silardg/VESA-ESP/Docs/Images/IMG_1075.jpg

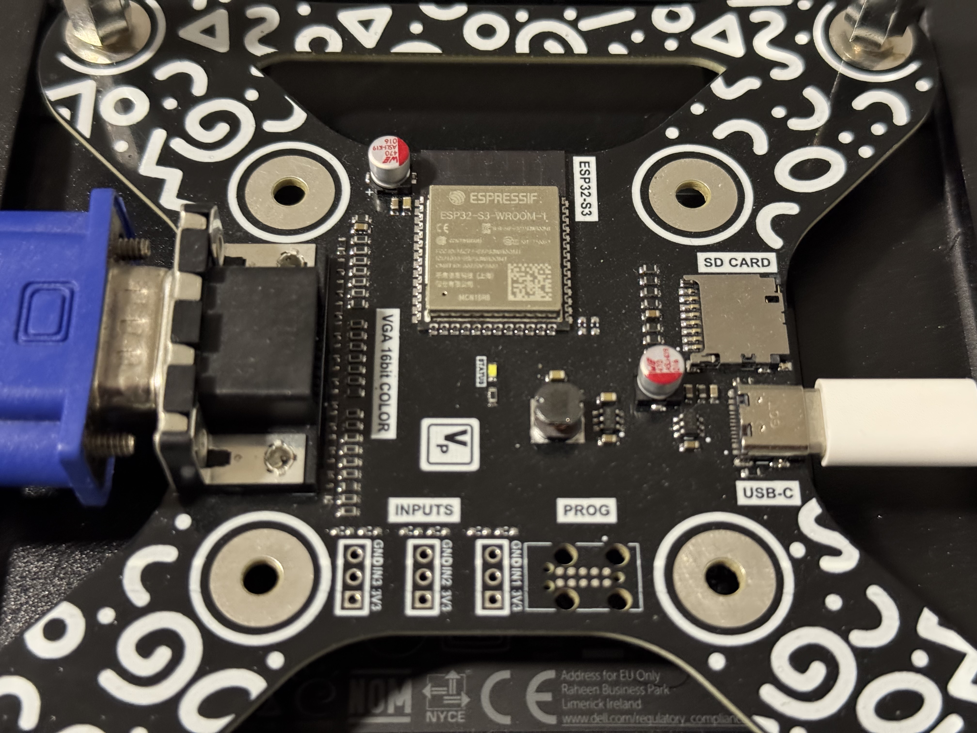
Docs/Images/IMG_1075.jpg
