silardg/VESA-ESP/Docs/Images/IMG_1078.jpg

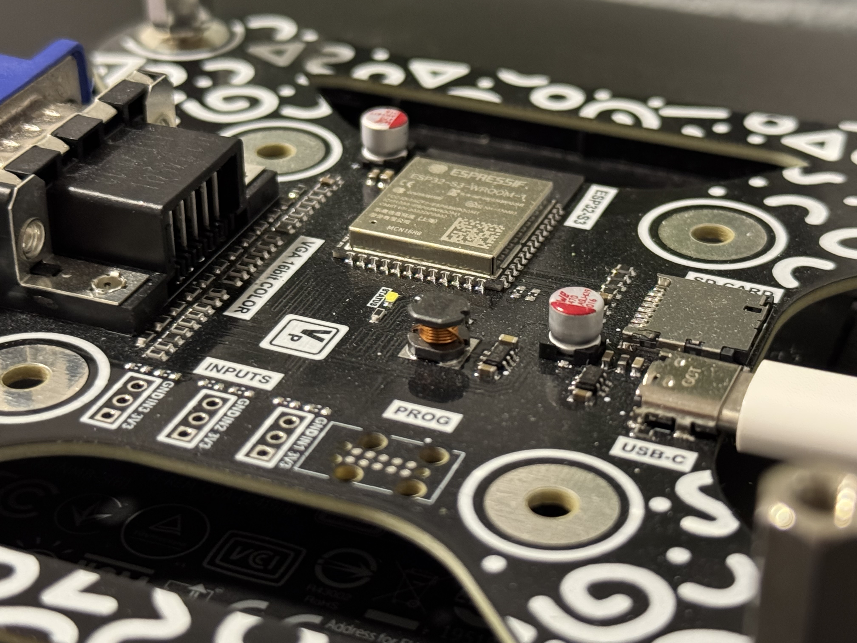
Docs/Images/IMG_1078.jpg
